master-gong/TmallGenieExtend/App/qndriver.c

#include "qndriver.h"


extern UINT8 QND_ReadReg(UINT8 adr);
extern UINT8 QND_WriteReg(UINT8 adr, UINT8 value);


#define R_TXRX_MASK    0x20
UINT8   qnd_Crystal = QND_CRYSTAL_DEFAULT;
UINT8   qnd_PrevMode;
UINT8   qnd_Country  = COUNTRY_CHINA ;
UINT16  qnd_CH_START = 7600;
UINT16  qnd_CH_STOP  = 10800;
UINT8   qnd_CH_STEP  = 1;


/**********************************************************************
void QNF_SetRegBit(UINT8 reg, UINT8 bitMask, UINT8 data_val)
**********************************************************************
Description: set register specified bit

Parameters:
    reg:        register that will be set
    bitMask:    mask specified bit of register
    data_val:    data will be set for specified bit
Return Value:
    None
**********************************************************************/
void QNF_SetRegBit(UINT8 reg, UINT8 bitMask, UINT8 data_val) 
{
    UINT8 temp;
    temp = QND_ReadReg(reg);
    temp &= (UINT8)(~bitMask);
    temp |= data_val & bitMask;
//    temp |= data_val;
    QND_WriteReg(reg, temp);
}

/**********************************************************************
UINT16 QNF_GetCh()
**********************************************************************
Description: get current channel frequency

Parameters:
    None
Return Value:
    channel frequency
**********************************************************************/
UINT16 QNF_GetCh() 
{
    UINT8 tCh;
    UINT8  tStep; 
    UINT16 ch = 0;
    // set to reg: CH_STEP
    tStep = QND_ReadReg(CH_STEP);
    tStep &= CH_CH;
    ch  =  tStep ;
    tCh= QND_ReadReg(CH);    
    ch = (ch<<8)+tCh;
    return CHREG2FREQ(ch);
}

/**********************************************************************
UINT8 QNF_SetCh(UINT16 freq)
**********************************************************************
Description: set channel frequency 

Parameters:
    freq:  channel frequency to be set
Return Value:
    1: success
**********************************************************************/
UINT8 QNF_SetCh(UINT16 freq) 
{
    // calculate ch parameter used for register setting
    UINT8 tStep;
    UINT8 tCh;
    UINT16 f; 
        f = FREQ2CHREG(freq); 
        // set to reg: CH
        tCh = (UINT8) f;
        QND_WriteReg(CH, tCh);
        // set to reg: CH_STEP
        tStep = QND_ReadReg(CH_STEP);
        tStep &= ~CH_CH;
        tStep |= ((UINT8) (f >> 8) & CH_CH);
        QND_WriteReg(CH_STEP, tStep);

    return 1;
}

/**********************************************************************
void QNF_SetAudioMono(UINT8 modemask, UINT8 mode) 
**********************************************************************
Description:    Set audio output to mono.

Parameters:
  modemask: mask register specified bit
  mode
        QND_RX_AUDIO_MONO:    RX audio to mono
        QND_RX_AUDIO_STEREO:  RX audio to stereo    
        QND_TX_AUDIO_MONO:    TX audio to mono
        QND_TX_AUDIO_STEREO:  TX audio to stereo 
Return Value:
  None
**********************************************************************/
void QNF_SetAudioMono(UINT8 modemask, UINT8 mode) 
{
    QNF_SetRegBit(SYSTEM2,modemask, mode);
}

/**********************************************************************
int QND_Delay()
**********************************************************************
Description: Delay for some ms, to be customized according to user
             application platform

Parameters:
        ms: ms counts
Return Value:
        None
            
**********************************************************************/
void QND_Delay(UINT16 ms) 
{
    UINT16 i,k;
    for(i=0; i<3000;i++) 
    {    
        for(k=0; k<ms; k++) 
        {

        }
    }
}

/**********************************************************************
void QN_ChipInitialization()
**********************************************************************
Description: chip first step initialization, called only by QND_Init()

Parameters:
    None
Return Value:
    None
**********************************************************************/
void QN_ChipInitialization()
{
    // reset
    QND_WriteReg(0x00,0x80);
    QND_Delay(20);
    //to be customized: change the crystal setting, according to HW design
    //.........
    //recalibration
    QNF_SetRegBit(0x00,0x40,0x40);
    QNF_SetRegBit(0x00,0x40,0x00);
    QND_Delay(20);                //delay 20 ms
    QND_WriteReg(0x18,0xe4);        //reset
    QND_WriteReg(0x1b,0xf0);    
    //Done chip recalibration
}

/**********************************************************************
int QND_Init()
**********************************************************************
Description: Initialize device to make it ready to have all functionality ready for use.

Parameters:
    None
Return Value:
    1: Device is ready to use.
    0: Device is not ready to serve function.
**********************************************************************/
UINT8 QND_Init() 
{
    QN_ChipInitialization();
//    QND_WriteReg(0x00,  0x01); //resume original status of chip /* 2008 06 13 */
    return 1;
}

/**********************************************************************
void QND_SetSysMode(UINT16 mode)
***********************************************************************
Description: Set device system mode(like: sleep ,wakeup etc) 
Parameters:
    mode:  set the system mode , it will be set by  some macro define usually:
    
    SLEEP (added prefix: QND_MODE_, same as below):  set chip to sleep mode
    WAKEUP: wake up chip 
    TX:     set chip work on TX mode
    RX:     set chip work on RX mode
    FM:     set chip work on FM mode
    AM:     set chip work on AM mode
    TX|FM:  set chip work on FM,TX mode
    RX|AM;  set chip work on AM,RX mode
    RX|FM:    set chip work on FM,RX mode
Return Value:
    None     
**********************************************************************/
void QND_SetSysMode(UINT16 mode) 
{    
    UINT8 val;
    switch(mode)        
    {        
    case QND_MODE_SLEEP:                       //set sleep mode        
        QNF_SetRegBit(SYSTEM1, R_TXRX_MASK, 0); 
        break;        
    default:    
            val = (UINT8)(mode >> 8);        
            if (val)
            {
                val = val >> 1;
                if (val & 0x20)
                {
                    // set to new mode if it's not same as old
                    if((QND_ReadReg(SYSTEM1) & R_TXRX_MASK) != val)
                    {
                        QNF_SetRegBit(SYSTEM1, R_TXRX_MASK, val); 
                    }
                    // make sure it's working on analog output
                    QNF_SetRegBit(SYSTEM1, 0x08, 0x00);    
                }
            }    
        break;        
    }    
}

/**********************************************************************
void QND_TuneToCH(UINT16 ch)
**********************************************************************
Description: Tune to the specific channel. call QND_SetSysMode() before 
call this function
Parameters:
    ch
    Set the frequency (10kHz) to be tuned,
    eg: 101.30MHz will be set to 10130.
Return Value:
    None
**********************************************************************/
void QND_TuneToCH(UINT16 ch) 
{
    QNF_SetCh(ch);
}

/**********************************************************************
void QND_SetCountry(UINT8 country)
***********************************************************************
Description: Set start, stop, step for RX and TX based on different
             country
Parameters:
country:
Set the chip used in specified country:
    CHINA:
    USA:
    JAPAN:
Return Value:
    None     
**********************************************************************/
void QND_SetCountry(UINT8 country) 
{
    qnd_Country = country;
    switch(country)
    {
    case COUNTRY_CHINA:
        qnd_CH_START = 7600;
        qnd_CH_STOP = 10800;
        qnd_CH_STEP = 1;
        break;
    case COUNTRY_USA:
        qnd_CH_START = 8810;
        qnd_CH_STOP = 10790;
        qnd_CH_STEP = 2;
        break;
    case COUNTRY_JAPAN:
        break;
    }
}

/**********************************************************************
UINT8 QND_TXSetPower( UINT8 gain)
**********************************************************************
Description:    Sets FM transmit power attenuation.

Parameters:
    gain: The transmission power attenuation value, for example, 
          setting the gain = 0x13, TX attenuation will be -6db
          look up table see below
BIT[5:4]
            00    0db
            01    -6db
            10    -12db
            11    -18db
BIT[3:0]    unit: db
            0000    124
            0001    122.5
            0010    121
            0011    119.5
            0100    118
            0101    116.5
            0110    115
            0111    113.5
            1000    112
            1001    110.5
            1010    109
            1011    107.5
            1100    106
            1101    104.5
            1110    103
            1111    101.5
for example:
  0x2f,    //111111    89.5
  0x2e,    //111110    91
  0x2d,    //111101    92.5
  0x2c,    //111100    94
  0x1f,    //111011 95.5
  0x1e,    //111010 97
  0x1d,    //111001 98.5
  0x1c,    //111000 100
  0x0f,    //001111    101.5
  0x0e,    //001110    103
  0x0d,    //001101    104.5
  0x0c,    //001100    106
  0x0b,    //001011    107.5
  0x0a,    //001010    109
  0x09,    //001001    110.5
  0x08,    //001000    112
  0x07,    //000111    113.5
  0x06,    //000110    115
  0x05,    //000101    116.5
  0x04,    //000100    118
  0x03,    //000011    119.5
  0x02,    //000010    121
  0x01,    //000001    122.5
  0x00     //000000    124
**********************************************************************/
void QND_TXSetPower( UINT8 gain)
{
    UINT8 value = 0;
    value |= 0x40;  
    value |= gain;
    QND_WriteReg(PAG_CAL, value);
}

/**********************************************************************
void QND_TXConfigAudio(UINT8 optiontype, UINT8 option )
**********************************************************************
Description: Config the TX audio (eg: volume,mute,etc)
Parameters:
  optiontype:option :
    QND_CONFIG_AUTOAGC:¡®option'set auto AGC, 0:disable auto AGC,1:enable auto AGC.
    QND_CONFIG_SOFTCLIP;¡®option¡¯set softclip,0:disable soft clip, 1:enable softclip.
    QND_CONFIG_MONO;¡®option¡¯set mono,0: QND_AUDIO_STEREO, 1: QND_AUDIO_STEREO
    QND_CONFIG_AGCGAIN;¡®option¡¯set AGC gain, range:0000~1111
Return Value:
  none
**********************************************************************/
void QND_TXConfigAudio(UINT8 optiontype, UINT8 option )
{
    switch(optiontype)
    {
    case QND_CONFIG_MONO:
        if (option)
            QNF_SetAudioMono(0x10, QND_TX_AUDIO_MONO);
        else
            QNF_SetAudioMono(0x10, QND_TX_AUDIO_STEREO);
        break;

    case QND_CONFIG_MUTE:
        if (option) 
            QNF_SetRegBit(23, 0x30,0);
        else    
            QNF_SetRegBit(23, 0x30,0x30);
        break;
    case QND_CONFIG_AGCGAIN:
        QNF_SetRegBit(0x04, 0x70,(UINT8)(option<<4));
        break;
    default:
        break;
    }
}

/**********************************************************************
UINT8 QND_RDSEnable(UINT8 mode) 
**********************************************************************
Description: Enable or disable chip to work with RDS related functions.
Parameters:
          on: QND_RDS_ON:  Enable chip to receive/transmit RDS data.
                QND_RDS_OFF: Disable chip to receive/transmit RDS data.
Return Value:
           QND_SUCCESS: function executed
**********************************************************************/
UINT8 QND_RDSEnable(UINT8 on) 
{
    UINT8 val;

    QND_LOG("=== QND_SetRDSMode === ");
    // get last setting
    val = QND_ReadReg(0x12);
    if (on == QND_RDS_ON) 
    {
        val |= RDSEN;
    } 
    else if (on == QND_RDS_OFF)
    {
        val &= ~RDSEN;
    }
    else 
    {
        return 0;
    }
    QND_WriteReg(0x12, val);
    return 1;
}

/**********************************************************************
void QND_RDSHighSpeedEnable(UINT8 on) 
**********************************************************************
Description: Enable or disable chip to work with RDS related functions.
Parameters:
  on: 
    1: enable 4x rds to receive/transmit RDS data.
    0: disable 4x rds, enter normal speed.
Return Value:
  none
**********************************************************************/
void QND_RDSHighSpeedEnable(UINT8 on) 
{
    QNF_SetRegBit(0x2, 0x40, on?0x40:0x00);
}

/**********************************************************************
UINT8 QND_DetectRDSSignal(void)
**********************************************************************
Description: detect the RDSS signal .

Parameters:
    None
Return Value:
    the value of STATUS3
**********************************************************************/
UINT8 QND_RDSDetectSignal(void) 
{
    return 0;
}

/**********************************************************************
void QND_RDSLoadData(UINT8 *rdsRawData, UINT8 upload)
**********************************************************************
Description: Load (TX) or unload (RX) RDS data to on-chip RDS buffer. 
             Before calling this function, always make sure to call the 
             QND_RDSBufferReady function to check that the RDS is capable 
             to load/unload RDS data.
Parameters:
  rdsRawData : 
    8 bytes data buffer to load (on TX mode) or unload (on RXmode) 
    to chip RDS buffer.
  Upload:   
    1-upload
    0--download
Return Value:
    QND_SUCCESS: rds data loaded to/from chip
**********************************************************************/
void QND_RDSLoadData(UINT8 *rdsRawData, UINT8 upload) 
{
    UINT8 i;
    //UINT8 temp;
    if (upload) 
    {       //TX MODE
        for (i = 0; i <= 7; i++) 
        {
            QND_WriteReg(RDSD0 + i, rdsRawData[i]);
        }    
    } 
}

/**********************************************************************
UINT8 QND_RDSCheckBufferReady(void)
**********************************************************************
Description: Check chip RDS register buffer status before doing load/unload of
RDS data.

Parameters:
    None
Return Value:
    QND_RDS_BUFFER_NOT_READY: RDS register buffer is not ready to use.
    QND_RDS_BUFFER_READY: RDS register buffer is ready to use. You can now
    load (for TX) or unload (for RX) data from/to RDS buffer
**********************************************************************/
UINT8 QND_RDSCheckBufferReady(void) 
{
    if (QND_ReadReg(SYSTEM1) & TXREQ) 
    {       
        //TX MODE
        QND_WriteReg(SYSTEM2,QND_ReadReg(SYSTEM2)^RDSTXRDY);  
        return QND_RDS_BUFFER_READY;
    }
    return QND_RDS_BUFFER_NOT_READY;
}
